lewipewi/leakwatch/sims/cable_ceiling.asc

C1: cap; 200p
R1: res; 10Meg
R2: res; 1k
V1: voltage; ""; AC 1
Named nets: Vout, 0
.ac dec 100 1 1Meg
.meas AC value_10hz  FIND mag(V(Vout)/(-I(V1))) AT 10
.meas AC value_100hz  FIND mag(V(Vout)/(-I(V1))) AT 100
.meas AC value_1000hz  FIND mag(V(Vout)/(-I(V1))) AT 1000
