lewipewi/leakwatch/sims/divider_vs_tia.asc

C1: cap; 330p
C2: cap; 330p
R1: res; 1Meg
R2: res; 1Meg
R3: res; 1Meg
R4: res; 1Meg
U1: UniversalOpAmp2
V1: voltage; ""; AC 1
V2: voltage; ""; AC 1
V3: voltage; 5
V4: voltage; -5
Named nets: divout, 0, tiaout
.ac dec 100 1 1Meg
.meas AC div3db WHEN mag(V(divout))=0.35355
.meas AC tia3db WHEN mag(V(tiaout))=0.70711
