lewipewi/leakwatch/sims/electrode_floor.asc

C1: cap; 0.5µ
C2: cap; 0.5µ
R1: res; 1k
R2: res; 100k
R3: res; 100
R4: res; 100k
V1: voltage; ""; AC 1
Named nets: probe, w1, w2, 0
.ac dec 100 0.1 10Meg
