lewipewi/leakwatch/sims/probe_circuit.asc

C1: cap; 0.5µ
C2: cap; 0.5µ
C3: cap; 200p
C4: cap; {CFB}
R2: res; 100k
R3: res; {RSOL}
R4: res; 100k
Rf: res; {RFB}
U1: UniversalOpAmp2
V1: voltage; ""; AC 1
V2: voltage; 5
V3: voltage; -5
Named nets: drive, w1, w2, 0, sense, out
.param RFB=4.7e6
.param CFB=3p
.step param RSOL list 200 2k 20k 200k 2meg 20meg
.ac dec 100 0.1 20Meg
.meas AC z10   FIND 4.7e6/mag(V(out)) AT 10
.meas AC z100  FIND 4.7e6/mag(V(out)) AT 100
.meas AC z1k   FIND 4.7e6/mag(V(out)) AT 1000
.meas AC z20k  FIND 4.7e6/mag(V(out)) AT 20000
.meas AC z1   FIND 4.7e6/mag(V(out)) AT 1
